UNIT-Electronics-MX/unit_devlab_temt6000_ambient_light_sensor/docs/hardware/index.html

UNIT Electronics · DevLab

# UNIT ATOM TEMT6000

Direct links to hardware documentation and product files for use in external platforms.

15 files 9 images 5 formats 15.3 MB total

Search hardware resources

## Product documents

4 files

DOCX 3.1 MB

### Product Reference

Editable product reference

unit_product_reference_v_1_1_0_atom_temt6000_ambient_light_sensor.docx

Copy link Open file

PDF 4.0 MB

### Product Reference

Publication-ready product reference

unit_product_reference_v_1_1_0_atom_temt6000_ambient_light_sensor.pdf

Copy link Open file

PDF 51.3 KB

### Schematic

Electrical schematic

unit_sch_v_2_0_0_ue0098_temt6000.pdf

Copy link Open file

PNG 220.3 KB

### Schematic

Electrical schematic

resources/unit_schematic_v_2_0_0_ue0098_temt6000.png

Copy link Open file

## Pinouts

3 files

JPG 1.8 MB

### Pinout — English

Connector and signal reference in English

resources/unit_pinout_v_3_1_0_ue0098_temt6000_ambient_light_sensor_en.jpg

Copy link Open file

PDF 1.6 MB

### Pinout — English

Connector and signal reference in English

unit_pinout_v_3_1_0_ue0098_temt6000_ambient_light_sensor_en.pdf

Copy link Open file

PDF 1.6 MB

### Pinout — Spanish

Connector and signal reference in Spanish

unit_pinout_v_3_1_0_ue0098_temt6000_ambient_light_sensor_es.pdf

Copy link Open file

## Board views

4 files

PNG 1.5 MB

### Board Topology

Functional board layout

resources/unit_topology_v_3_1_0_ue0098_temt6000_ambient_light_sensor.png

Copy link Open file

PNG 32.5 KB

### Bottom View

Bottom-side board view

resources/unit_btm_v_0_3_1_ue0098_temt6000.png

Copy link Open file

PNG 1.1 MB

### Mechanical Dimensions

Board outline and dimensions

resources/unit_dimensions_v_3_1_0_ue0098_temt6000_ambient_light_sensor.png

Copy link Open file

PNG 32.5 KB

### Top View

Top-side board view

resources/unit_top_v_0_3_1_ue0098_temt6000.png

Copy link Open file

## Other resources

4 files

JPG 114.0 KB

### Conn

Hardware resource

resources/wiki/Conn.jpg

Copy link Open file

MD 5.0 KB

### Hardware README

Hardware overview and source notes

README.md

Copy link Open file

PNG 24.0 KB

### Library

Hardware resource

resources/wiki/library.png

Copy link Open file

PNG 171.1 KB

### Mode

Hardware resource

resources/wiki/mode.png

Copy link Open file

No resources match your search.

UNIT Electronics hardware resources
