UNIT-Electronics-MX/unit_devlab_temt6000_ambient_light_sensor/tools/product-reference/assets/functional-block-diagram.png

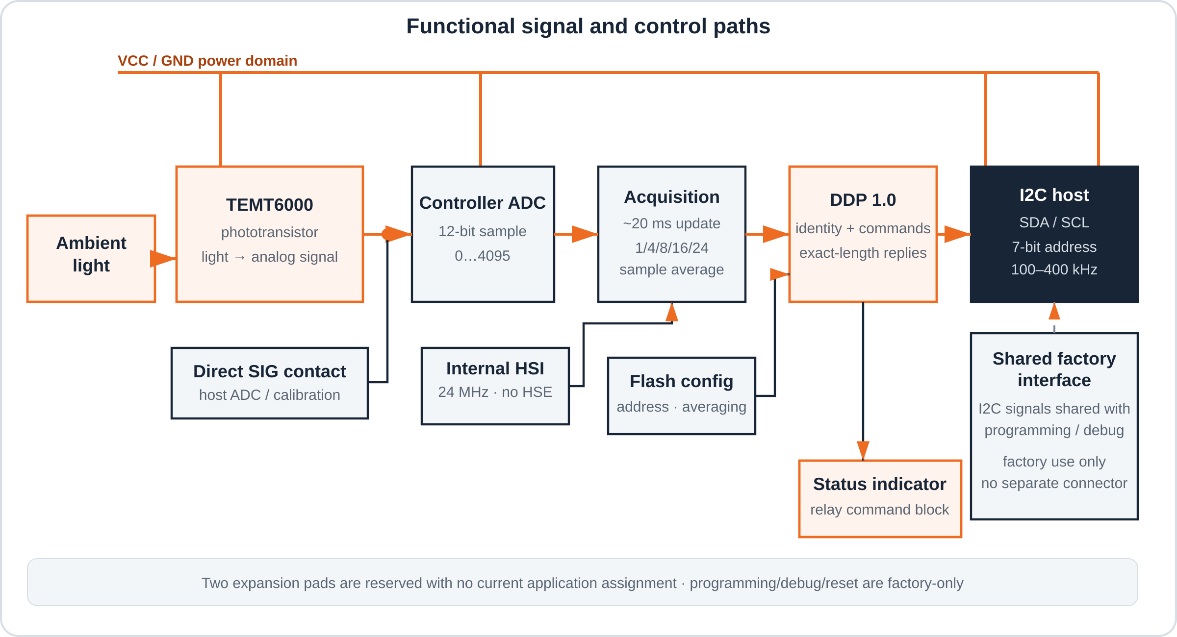
tools/product-reference/assets/functional-block-diagram.png
