UNIT-Electronics-MX/unit_devlab_temt6000_ambient_light_sensor/tools/product-reference/assets/unit_top_v_0_3_1_ue0098_temt6000.png

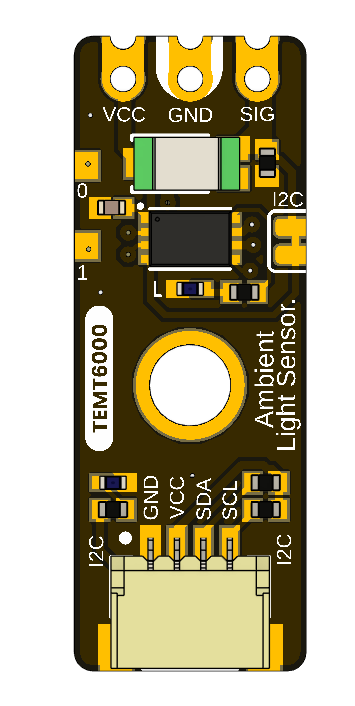
tools/product-reference/assets/unit_top_v_0_3_1_ue0098_temt6000.png
